leomancini/claude-handset/patch-renders/caps_amp_before.png

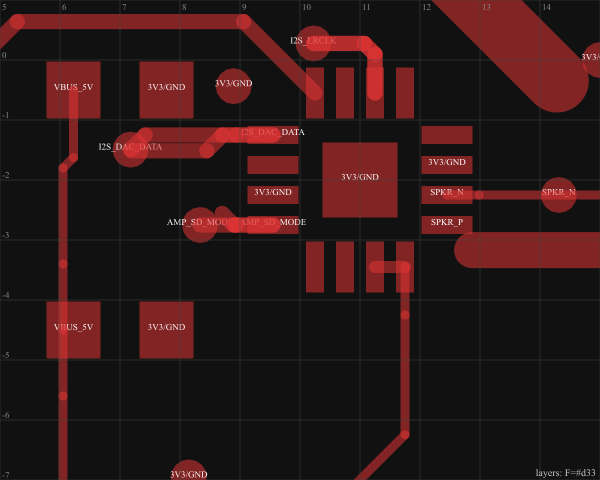
patch-renders/caps_amp_before.png
