leomancini/claude-handset/patch-renders/caps_north_after.png

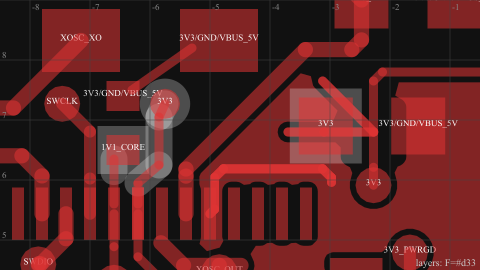
patch-renders/caps_north_after.png
