leomancini/claude-handset/patch-renders/orig_caps_F.png

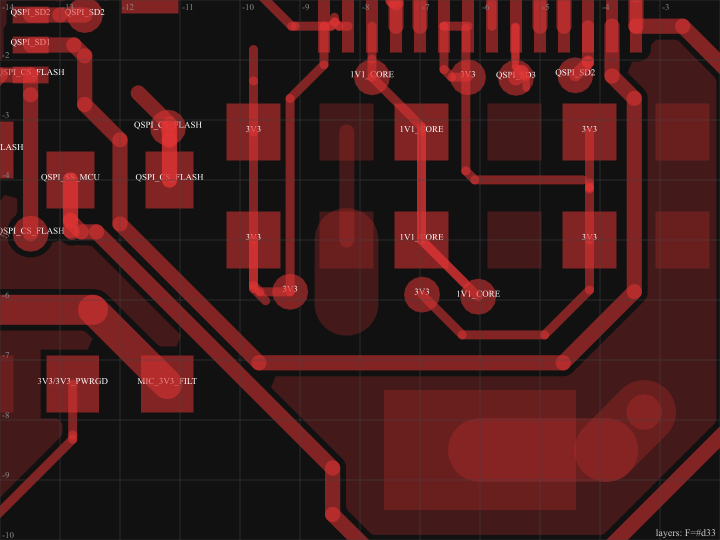
patch-renders/orig_caps_F.png
