leomancini/claude-handset/patch-renders/site_caps_F.png

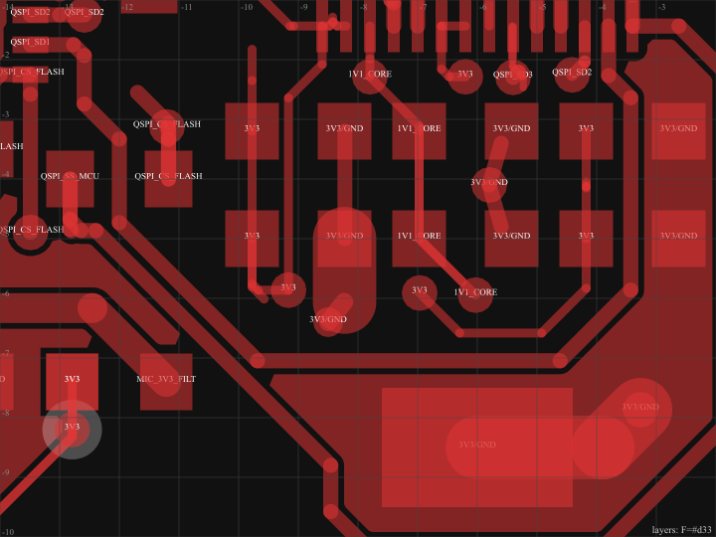
patch-renders/site_caps_F.png
