leomancini/claude-handset/patch-renders/site_caps_In1.png

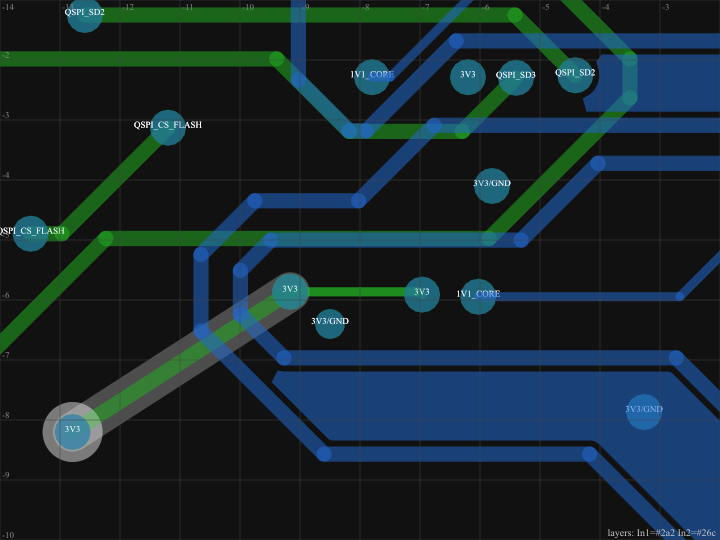
patch-renders/site_caps_In1.png
