leomancini/claude-handset/patch-renders/site_short_F.png

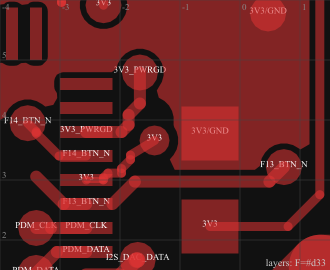
patch-renders/site_short_F.png
