leomancini/claude-handset/original-flux-export/BOM/leomancini-claude-handset-BOM-V3cf75256-Seeed.csv

Designator | Manufacturer Part Number or Seeed SKU | QTY | Link
C1,C2,C25,C3 |  | 4
C10,C11,C15,C16,C17,C20,C24,C28,C4,C5,C6,C7,C8,C9 |  | 14
C12,C18 |  | 2
C13,C14 |  | 2
C29 |  | 1
D1 | USBLC6-2SC6 | 1
D2 | SMF5.0A | 1
F1 | SMD050F-2 | 1
FB1 | BLM18AG601SN1D | 1
J1 | USB4105-GF-A | 1
J3 | S2B-PH-K-S(LF)(SN) | 1
J4 | FTSH-103-01-L-DV | 1
MK1 | SPH0641LU4H-1 | 1
R1,R2 |  | 2
R3,R4 |  | 2
R5,R6 |  | 2
R14,R15,R7,R8,R9 |  | 5
SW1,SW2 | B3U-3000P | 2
SW3,SW4 | TS-1088-AR02016 | 2
U1 | RP2040 | 1
U2 | W25Q16JVUXIQ | 1
U3 | MAX98357AETE+T | 1
U5 | MCP1825T-3302E/DC | 1
Y1 | ABM8-272-T3 | 1
